ImageBlue/PID_exp_platform/Ocontroller/mainwindow.h

#ifndef MAINWINDOW_H
#define MAINWINDOW_H

#include <QMainWindow>
#include <QtSerialPort/QSerialPort>
#include <QtSerialPort/QSerialPortInfo>
#include <QChartView>
#include <QtCharts>
#include <QString>
#include <iostream>
#include <QTimer>
#include <QTime>
#include <QDebug>
#include <QBitArray>
#include <QMessageBox>
#include <QByteArray>
#include <QThread>
#include "AsyncSerialPort.h"
#include "AsyncMQTT.h"

QT_BEGIN_NAMESPACE
namespace Ui { class MainWindow; }
QT_END_NAMESPACE

class MainWindow : public QMainWindow
{
    Q_OBJECT

public:
    MainWindow(QWidget *parent = nullptr);
    ~MainWindow();

private slots:

    void on_CloseButton_clicked();

    void on_SetNewButton_clicked();

    void on_VNewButton_clicked();

    void on_ConnectSerialButton_clicked();

    void on_SearchSeiralButton_clicked();

    void on_CloseSerialButton_clicked();

    void sleep(int msec);       //延时函数

    void SerialPort_Receive(QByteArray buffer);

    void on_ClearButton_clicked();

    void Paint_Data();

    void on_WLConnectButton_clicked();

    void on_WLDisconnectButton_clicked();

    void MQTT_Receive(QByteArray buffer);

    void on_ManuRButton_clicked();

    void on_AutoRButton_clicked();

private:
    Ui::MainWindow *ui;
    //QSerialPort* SerialPort;

    QTimer* ConnectSerialTimer;
    QTimer* writetimer;
    QTimer* painttimer;

    QChart *chart;
    QChartView *chartView;
    QValueAxis *AxisXT;        //时间坐标
    QValueAxis *AxisYV;        //实时流速坐标
    QSplineSeries *sSeriesV;

    //QDateTime curTime;
    QString strTime;

    AsyncSerialPort *ASerialPort;

    AsyncMQTT *AMqtt;

signals:
    void Send_to_SerialPort(QString qstrS);
    void Send_to_MQTT(QString qstrS);
};
#endif // MAINWINDOW_H
